theairboard/TheAirBoard/android/tAB-Direction/tAB-Direction.png

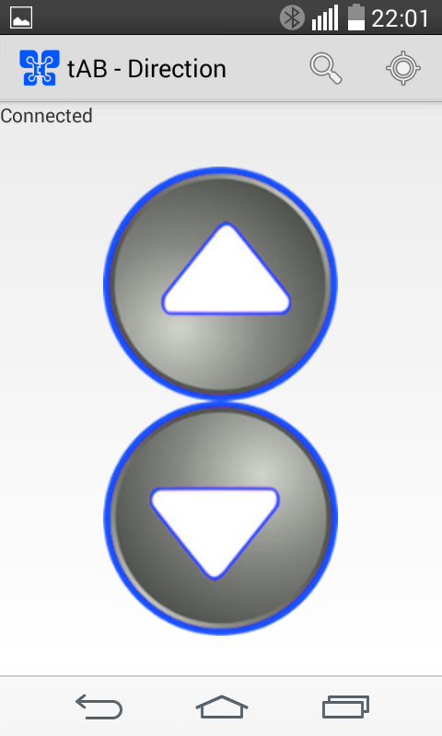
android/tAB-Direction/tAB-Direction.png
