theairboard/TheAirBoard/eagle/Altimeter-Barometer/Altimeter-Barometer.sch

## EAGLE design eagle/Altimeter-Barometer/Altimeter-Barometer.sch (2014-11-30)

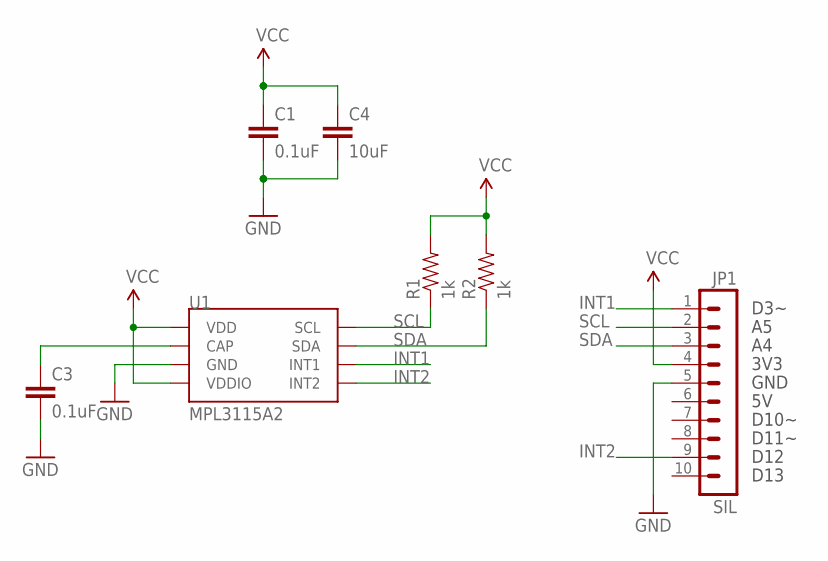
[picture p9: schematic Altimeter-Barometer.sch]

Parts:
C1, C3: 0.1uF; 0603-CAP
C4: 10uF; 0805
JP1: SIL; SIL-1X10
R1, R2: 1k; 0603-RES
U1: MPL3115A2; LGA8

Connections:
CAP: C3.1, U1.2 (CAP)
GND: C1.2, C3.2, C4.2, JP1.5, U1.3 (GND)
INT1: JP1.1, U1.6 (INT1)
INT2: JP1.9, U1.5 (INT2)
SCL: JP1.2, R1.1, U1.8 (SCL)
SDA: JP1.3, R2.1, U1.7 (SDA)
VCC: C1.1, C4.1, JP1.4, R1.2, R2.2, U1.1 (VDD), U1.4 (VDDIO)

Notes on the sheet:
D3~
3V3
GND
D10~
D11~
D12
D13
