theairboard/TheAirBoard/eagle/Temperature-Humidity/Temperature-Humidity.sch

## EAGLE design eagle/Temperature-Humidity/Temperature-Humidity.sch (2014-11-30)

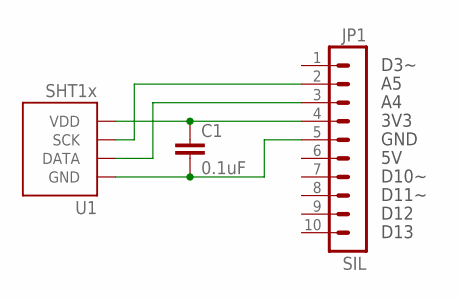
[picture p10: schematic Temperature-Humidity.sch]

Parts:
C1: 0.1uF; 0603-CAP
JP1: SIL; SIL-1X10
U1: SHT1x; SHT1X

Connections:
GND: C1.2, JP1.5, U1.1 (GND)
unnamed: JP1.2, U1.3 (SCK)
unnamed: JP1.3, U1.2 (DATA)
VDD: C1.1, JP1.4, U1.4 (VDD)

Notes on the sheet:
D3~
3V3
GND
D10~
D11~
D12
D13
