theairboard/TheAirBoard/arduino/WiFlySerial/WiFlySerial.h

#ifndef __WIFLYSERIAL_H__
#define __WIFLYSERIAL_H__

/*
Arduino WiFly Device Driver
Driver for Roving Network's WiFly GSX (c) (tm) b/g WiFi device
 using a simple Tx/Rx serial connection.
 4-wires needed: Power, Gnd, Rx, Tx

Provides moderately-generic WiFi device interface.
Compatible with Arduino 1.0
Version 1.08

- WiFlyGSX is a relatively intelligent peer.
- WiFlyGSX may have awoken in a valid configured state while Arduino asleep; 
    initialization and configuration to be polite and obtain state
- WiFlyGSX hardware CTS/RTS not enabled yet
- Can listen on multiple ports, only one at a time.
- most settings assumed volatile; fetched from WiFly where reasonable.

Expected pattern of use:
begin
issue commands, such as set SSID, passphrase etc
exit command mode / enter data mode
listen for web activity
Open a TCP/UDP connection to a peer
send / receive data
close connection

SoftwareSerial is exposed as serial i/o

Credits:
  SoftwareSerial   Mikal Hart   http://arduiniana.org/
  Time             Michael Margolis http://www.arduino.cc/playground/uploads/Code/Time.zip
  WiFly            Roving Networks   www.rovingnetworks.com
  and to Massimo and the Arduino team.


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
Copyright GPL 2.0 Tom Waldock 2011
*/

#include <SoftwareSerial.h>
#include <Streaming.h>
#include <avr/pgmspace.h>

#define ARDUINO_RX_PIN  2
#define ARDUINO_TX_PIN  3


#define COMMAND_BUFFER_SIZE 64
#define SMALL_COMMAND_BUFFER_SIZE 20
#define RESPONSE_BUFFER_SIZE 80
#define INDICATOR_BUFFER_SIZE 16
#define IP_ADDR_WIDTH  18
#define UC_N_IP_BYTES  4      // number of bytes per IP Address (need test for IPv6)

// default ports as set in WiFly - if you change these, make certain you call setRemotePort/setLocalPort
#define WIFLY_DEFAULT_REMOTE_PORT 80    
#define WIFLY_DEFAULT_LOCAL_PORT 2000  
#define WIFLY_DEFAULT_BAUD_RATE 9600

#define COMMAND_MODE_GUARD_TIME 	300 // in milliseconds.  Must be at least 250ms.
#define DEFAULT_WAIT_TIME			1000UL  // waiting time for a command
#define ATTN_WAIT_TIME				1000UL  // waiting time for a reponse after a $$$ attention signal
#define JOIN_WAIT_TIME 				10000UL  // joining a network could take longer
#define SERVING_WAIT_TIME			300000UL   // 5 minutes default wait time for serving a connection in milliseconds
#define WIFLY_RESTART_WAIT_TIME		2000UL  // wait time after issuing reboot command.
#define WIFLY_TIME_SYNC_INTERVAL 	100UL   // 15 minute interval between clock resyncs
#define WIFLY_NTP_SYNC_INTERVAL     "60"    // sync with NTP server every hour


#define COMMAND_MODE_ENTER_RETRY_ATTEMPTS 5
#define COMMAND_RETRY_ATTEMPTS 3

// WiFly Responses  
#define PROMPT_NONE					0x0
#define PROMPT_EXPECTED_TOKEN_FOUND	0x1
#define PROMPT_READY 			   	0x2
#define PROMPT_CMD_MODE 	   		0x4
#define PROMPT_AOK 			    	0x8
#define PROMPT_OTHER 				0x10
#define PROMPT_CMD_ERR 				0x20
#define PROMPT_TIMEOUT 				0x40
#define PROMPT_OPEN 				0x80
#define PROMPT_CLOSE 				0x100
#define PROMPT_OPEN_ALREADY			0x200

#define N_PROMPTS 				9
#define WIFLY_MSG_EXPECTED  	0
#define WIFLY_MSG_AOK  			1
#define WIFLY_MSG_CMD  			2
#define WIFLY_MSG_ERR  			3
#define WIFLY_MSG_PROMPT  		4
#define WIFLY_MSG_PROMPT2  		5
#define WIFLY_MSG_CLOSE  		6
#define WIFLY_MSG_OPEN  		7
#define WIFLY_MSG_OPEN_ALREADY  8

// Auth Modes for Network Authentication
// See WiFly manual for details
#define WIFLY_AUTH_OPEN        0    // Open (default)  
#define WIFLY_AUTH_WEP         1    // WEP-128
#define WIFLY_AUTH_WPA1        2    // WPA1
#define WIFLY_AUTH_WPA1_2      3    // Mixed-mode WPA1 and WPA2-PSK
#define WIFLY_AUTH_WPA2_PSK    4    // WPA2-PSK
#define WIFLY_AUTH_ADHOC       6    // Ad-hoc, join any Ad-hoc network

// Join modes for joining networks
// See WiFly manual for details
#define WIFLY_JOIN_MANUAL      0    // Manual, do not try to join automatically
#define WIFLY_JOIN_AUTO        1    // Try to join the access point that matches the stored SSID, passkey and channel. (Default)
#define WIFLY_JOIN_ANY         2    // Join ANY access point with security matching the stored authentication mode. Ignores stored SSID and searches for strongest signal.
#define WIFLY_JOIN_MAKE_ADHOC  4    // Create an Ad-Hoc network using stored SSID, IP and netmask.  Channel MUST be set. DHCP should be 0. 

// DHCP modes
// See WiFly manual for details
#define WIFLY_DHCP_OFF         0    // DHCP OFF, use static IP address
#define WIFLY_DHCP_ON          1    // DHCP ON, get IP, gateway from Access Point.
#define WIFLY_DHCP_AUTO        2    // DHCP AUTO-IP, generally used with Adhoc networks
#define WIFLY_DHCP_CACHE       3    // DHCP CACHE, use previous IP address if lease is not expired.

// IP modes: UDP and TCP
#define WIFLY_IPMODE_UDP       0x02;    // Same as W5100_defn's SmMR::UDP
#define WIFLY_IPMODE_TCP       0x01;    // Same as W5100_defn's SmMR::TCP

#define WIFLY_STATUS_OFFLINE    0
#define WIFLY_STATUS_ONLINE     1



// WiFly-specific prompt codes
static char* WiFlyFixedPrompts[N_PROMPTS] = { "","AOK", "CMD", "ERR: ?", "",">","*CLOS*","*OPEN*","ERR:Connected" };
static byte  WiFlyFixedFlags[N_PROMPTS] = {PROMPT_EXPECTED_TOKEN_FOUND, PROMPT_AOK, PROMPT_CMD_MODE, PROMPT_CMD_ERR, PROMPT_READY,    	PROMPT_READY,PROMPT_CLOSE, PROMPT_OPEN, PROMPT_OPEN_ALREADY};

// Utility functions
char* IP_ArrayToBuffer( const uint8_t* pIP, char* pBuffer, int buflen);
uint8_t* BufferToIP_Array(char* pBuffer, uint8_t* pIP)  ;



class WiFlySerial : public Stream {
  public:
    // Constructors
    WiFlySerial(byte pinReceive, byte pinSend);
    
    // Destructor
    
    // Initialization
    boolean begin();  // Initialises this interface Class.
    
    // Status
    
    // Obtain current device status flags
    long    getDeviceStatus();  // refreshes device status flags.
    boolean isAssociated();
    boolean isTCPConnected();
    boolean isAuthenticated();
    boolean isifUp();
    int     getChannel();
    boolean isDNSfound();
    boolean isDNScontacted();
    boolean isInCommandMode();
    boolean isConnectionOpen();
            
    // Information
    // Device Info
    char* showNetworkScan( char* pNetScan, const int buflen);
    char* getLibraryVersion(char* buf, int buflen);

// IP info
    char* getSSID(char* buf, int buflen);
    char* getDeviceID(char* buf, int buflen);    
    char* getIP(char* buf, int buflen);
    char* getNetMask(char* buf, int buflen);
    char* getGateway(char* buf, int buflen);
    char* getDNS(char* buf, int buflen);
    char* getMAC(char* buf, int buflen);
    char* getNTP(char* buf, int buflen);
    char* getNTP_Update_Frequency(char* buf, int buflen);
    unsigned long getTime();
    char* getRSSI(char* pBuf, int buflen);
    char* getBattery(char* pBuf, int buflen);

    // Transmit / Receive / available through exposed SoftwareSerial
    SoftwareSerial uart;    
    
    // Configuration Generic Wifi methods
    
    // Generic Wifi methods
    boolean setSSID( const char* pSSID);    
    boolean setPassphrase( const char* pPassphrase);
    boolean setDeviceID( const char* pHostname);
    boolean setNTP(const char* pNTP_IP);
    boolean setNTP_Update_Frequency(const char* pFreq);
    boolean setNTP_UTC_Offset(float fltUTC_Offset_hours);
    boolean setIP( const char* pIP);
    boolean setNetMask( const char* pNM);
    boolean setGateway( const char* pGW);
    boolean setDNS( const char* pDNS);
    boolean setChannel( const char* pChannel);
    boolean setLocalPort( int iNewLocalPort = WIFLY_DEFAULT_LOCAL_PORT);
    boolean setRemotePort( int iNewRemotePort = WIFLY_DEFAULT_REMOTE_PORT);
    boolean setProtocol( unsigned int iProtocol);
    boolean setAuthMode( int iAuthMode);
    boolean setJoinMode( int iJoinMode);        
    boolean setDHCPMode(const int iModeDHCP);
    
    // wifi network Association
    
    // Joins ssid set with setSSID
    boolean join();
    boolean join( char* pSSID);
    
    // Leaves current SSID.
    boolean leave();
                 
    // Generic utility
    boolean StartCommandMode(char* pBuffer = NULL, const int bufSize = COMMAND_BUFFER_SIZE );
    boolean exitCommandMode();     
    void    reboot();
    
    // Client Connection
    boolean openConnection(const char* pURL, const unsigned long WaitTime = JOIN_WAIT_TIME  );
    boolean closeConnection(boolean bSafeClose = true);
    
    // Server Connection - waits for a client to connect
    boolean serveConnection(  const unsigned long reconnectWaitTIme = SERVING_WAIT_TIME );
    
    // Open-format for RN 131C/G commands
    boolean SendInquiry(char *Command, char* pBuffer, const int bufsize = RESPONSE_BUFFER_SIZE );
    boolean SendInquirySimple(char *Command);
    boolean SendCommand( char *Command,   char *SuccessIndicator, char* pBuffer, const int bufsize, 
                const boolean bCollecting = true, const unsigned long WaitTime = DEFAULT_WAIT_TIME , 
                const boolean bClear = true, const boolean bPromptAfterResult = true );
    boolean SendCommandSimple( char *Command,   char *SuccessIndicator);

    // utilities for collecting results or scanning for indicators.
    int     ScanForPattern( char* responseBuffer, const int bufsize, const char *pExpectedPrompt, 
                const boolean bCapturing = true, const unsigned long WaitTime = DEFAULT_WAIT_TIME, const boolean bPromptAfterResult = true   );
    char*   ExtractDetail(char* pCommand, char* pDetail, const int buflen, const char* pFrom, const char* pTo);
    char*   ExtractDetailIdx(const int idxCommand, char* pDetail, int buflen, const int idxSearch, const int idxStop);
    int     CaptureUntilPrompt( char* responseBuffer, const int bufsize, const char *pExpectedPrompt, const unsigned long WaitTime = DEFAULT_WAIT_TIME  );

    int peek();
    virtual size_t write(uint8_t byte);
    virtual int read();
    virtual int available();
    virtual void flush();
    
    int drain ();
  
    using Print::write;

    // debug utilities - use Serial : not NewSoftSerial as it will affect incoming stream.
    // should change these to use stream <<
    void    setDebugChannel( Print* pDebug);
    Print*  getDebugChannel( )  { return pDebugChannel; };
    void    clearDebugChannel();
    void    DebugPrint( const char* pMessage);
    void    DebugPrint( const int iNumber);
    void    DebugPrint( const char ch);


    
  private:
    // internal buffer for command-prompt
    char    szWiFlyPrompt[INDICATOR_BUFFER_SIZE ];
    
    // Internal status flags
    long    fStatus;        
    boolean bWiFlyInCommandMode;
    boolean bWiFlyConnectionOpen;
    char*   pControl;
    
    // Ports for connections
    int     iRemotePort;
    int     iLocalPort;
    long 	lUTC_Offset_seconds;
    

    boolean GetCmdPrompt();
    char*   GetBuffer_P(const int StringIndex, char* pBuffer, int bufSize);
    char*   ExtractLineFromBuffer(const int idString,  char* pBuffer, const int bufsize, const char* pStartPattern, const char* chTerminator);
    boolean issueSetting( int idxCommand, const char* pParam);

    // Internal debug channel.
    Print*  pDebugChannel;

};

// static  WiFlySerialv2 wifi ( ARDUINO_RX_PIN, ARDUINO_TX_PIN);

#endif
