theairboard/TheAirBoard/arduino/TheAirBoard/examples/NeoPixelsColors/NeoPixelsColors.ino

/*
Smartphone-controlled NEOPIXELS test program
- Test 7 colors of the built-in RGB LED at maximum power and 40 NeoPixels in 2 concentric rings:
NeoPixel Ring - 24 x WS2812 5050 RGB LED with Integrated Drivers
http://www.adafruit.com/products/1586
NeoPixel Ring - 16 x WS2812 5050 RGB LED with Integrated Drivers
http://www.adafruit.com/products/1463

On Bluetooth 4.0 BLE Android devices:
1. Install tAB-COLOR.apk
   http://github.com/theairboard/TheAirBoard/raw/master/arduino/TheAirBoard/examples/Color/tAB-COLOR.apk
2. Search and connect "Bluno" device

On Bluetooth 2 Android devices:
1. Install tAB-Colorbuttons.apk
   http://github.com/theairboard/TheAirBoard/raw/master/arduino/TheAirBoard/examples/Color/tAB-Colorbuttons.apk
2. Search and connect your device

The AirBoard is a thumb-size, Arduino-compatible, wireless, low-power,
ubiquitous computer designed to sketch Internet-of-Things, fast!
Visit http://www.theairboard.cc
Upload your first sketch in seconds from https://codebender.cc?referral_code=Ub56L825Qb
Check README.txt and license.txt for more information.
All text above must be included in any redistribution.
*/

#include <Adafruit_NeoPixel.h>
#include <TheAirBoard.h>

#define PIN            10       // output pin to drive Neopixels
#define NUMPIXELS      40       // Numper of Neopixels
#define LUX            255      // Neopixels power from 1 to 255

int i;
Adafruit_NeoPixel pixels = Adafruit_NeoPixel(NUMPIXELS, PIN, NEO_GRB + NEO_KHZ800);

// the setup routine runs once when you switch on the board:
void setup() {
  pinMode(RED, OUTPUT);         // initialize the RED LED pin as an output
  pinMode(GREEN, OUTPUT);       // initialize the GREEN LED pin as an output
  pinMode(BLUE, OUTPUT);        // initialize the BLUE LED pin as an output
  analogWrite(GREEN, 1);        // switch ON indicator at low power 
  pixels.begin();               // initialize Neopixels
  Serial.begin(115200);         // initialize serial communication at 115200 bauds for BLE, 9600 bauds for Bluetooth 2
}

// the loop routine runs over and over again forever:
void loop() { 
  while(Serial.available()) {
    switch(Serial.read()) {
      case 'a': // white
        digitalWrite(RED, 1); digitalWrite(GREEN, 1); digitalWrite(BLUE, 1);
        for(i=0; i<NUMPIXELS; i++){
            pixels.setPixelColor(i, pixels.Color(LUX, LUX, LUX));
        }
        break;
      case 'b': // yellow
        digitalWrite(RED, 1); digitalWrite(GREEN, 1); digitalWrite(BLUE, 0);
        for(i=0; i<NUMPIXELS; i++){
            pixels.setPixelColor(i, pixels.Color(LUX, LUX, 0));
        } 
        break;
      case 'c': // magenta
        digitalWrite(RED, 1); digitalWrite(GREEN, 0); digitalWrite(BLUE, 1);
        for(i=0; i<NUMPIXELS; i++){
            pixels.setPixelColor(i, pixels.Color(LUX, 0, LUX));
        }
        break;
      case 'd': // red
        digitalWrite(RED, 1); digitalWrite(GREEN, 0); digitalWrite(BLUE, 0);
        for(i=0; i<NUMPIXELS; i++){
            pixels.setPixelColor(i, pixels.Color(LUX, 0, 0));
        }
        break;
      case 'e': // cyan
        digitalWrite(RED, 0); digitalWrite(GREEN, 1); digitalWrite(BLUE, 1);
        for(i=0; i<NUMPIXELS; i++){
            pixels.setPixelColor(i, pixels.Color(0 , LUX, LUX));
        }
        break;
      case 'f': // green
        digitalWrite(RED, 0); digitalWrite(GREEN, 1); digitalWrite(BLUE, 0);
        for(i=0; i<NUMPIXELS; i++){
            pixels.setPixelColor(i, pixels.Color(0, LUX, 0));
        }
        break;
      case 'g': // blue
        digitalWrite(RED, 0); digitalWrite(GREEN, 0); digitalWrite(BLUE, 1);
        for(i=0; i<NUMPIXELS; i++){
            pixels.setPixelColor(i, pixels.Color(0, 0, LUX));
        }
        break;
      case 'h': //off
        digitalWrite(RED, 0); digitalWrite(GREEN, 0); digitalWrite(BLUE, 0);
        for(int i=0;i<NUMPIXELS;i++){
            pixels.setPixelColor(i, pixels.Color(0 , 0, 0));
        }
        break;
      default:
        break;
    }
    pixels.show();
  }
}
