theairboard/TheAirBoard/arduino/WiFlySerial/Examples/WiFly_Test/Credentials.h

#ifndef __CREDENTIALS_H__
#define __CREDENTIALS_H__

// Wifi parameters
char passphrase[] = ".^ZhN%i1wMRx E&<X<cpy7J DHsq euUz@H~vNlQ c-2v(4(PE-3|i,tVNVuLDT";
char ssid[] = "olivier";
char ntp_server[] = "nist1-la.ustiming.org"; // or your favorite ntp server.

#endif
